arnthorg/FSAE-car-dashboard-/myndir/IMG_20160512_113746.jpg

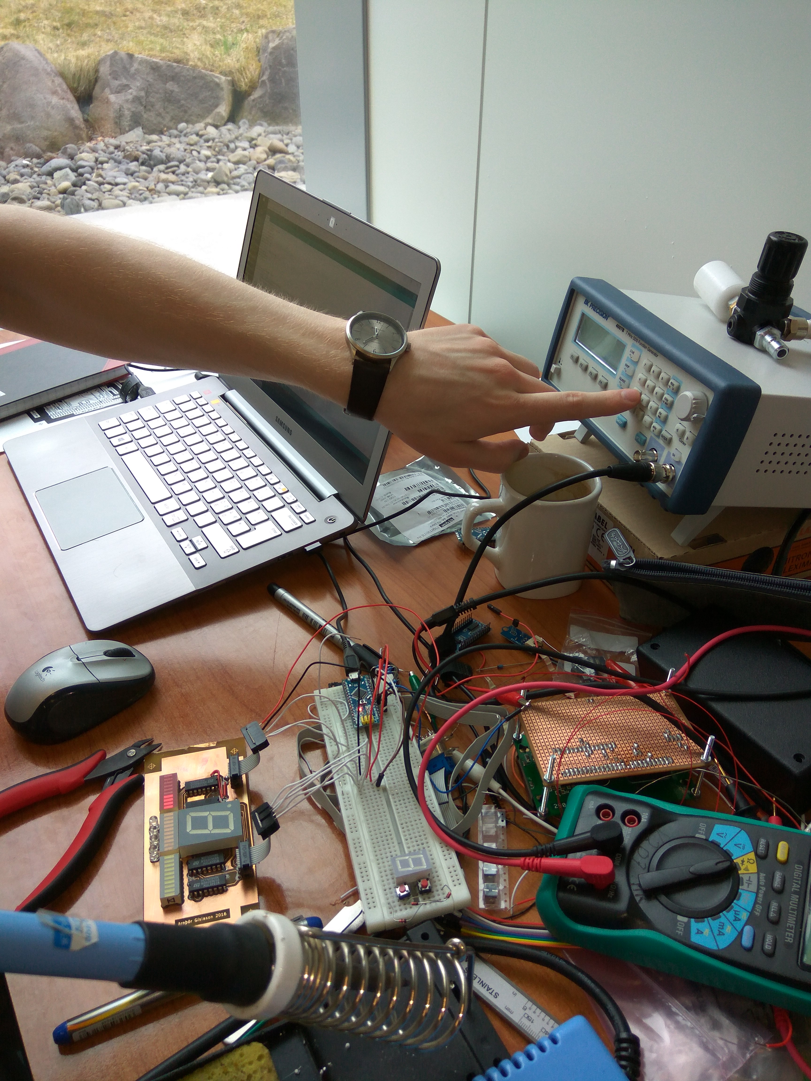
myndir/IMG_20160512_113746.jpg
