arnthorg/FSAE-car-dashboard-/myndir/IMG_20160512_135752.jpg

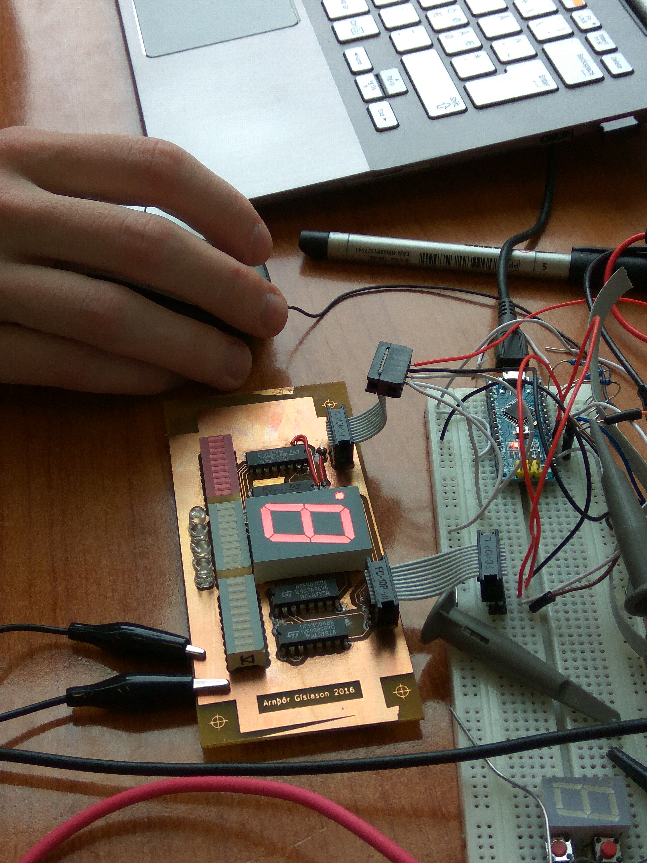
myndir/IMG_20160512_135752.jpg
