arnthorg/FSAE-car-dashboard-/myndir/IMG_20160516_171029.jpg

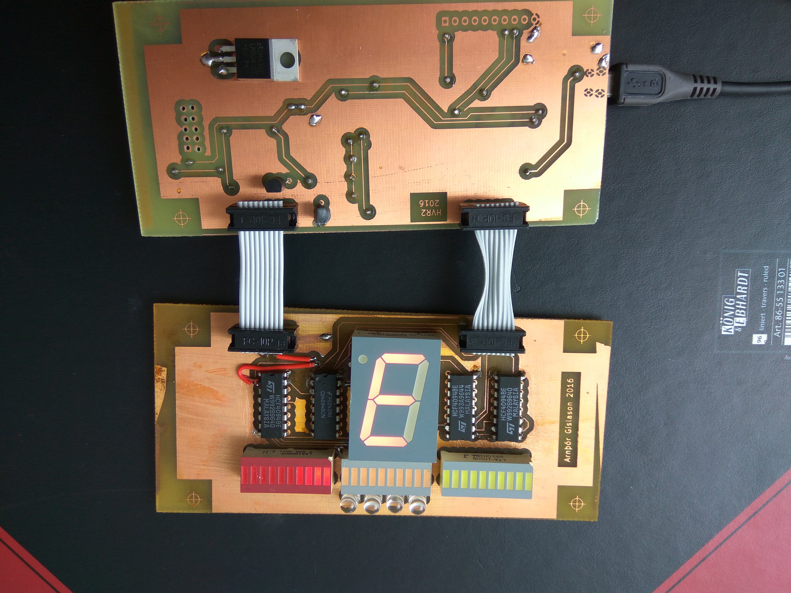
myndir/IMG_20160516_171029.jpg
