arnthorg/FSAE-car-dashboard-/myndir/IMG_20160512_113758.jpg

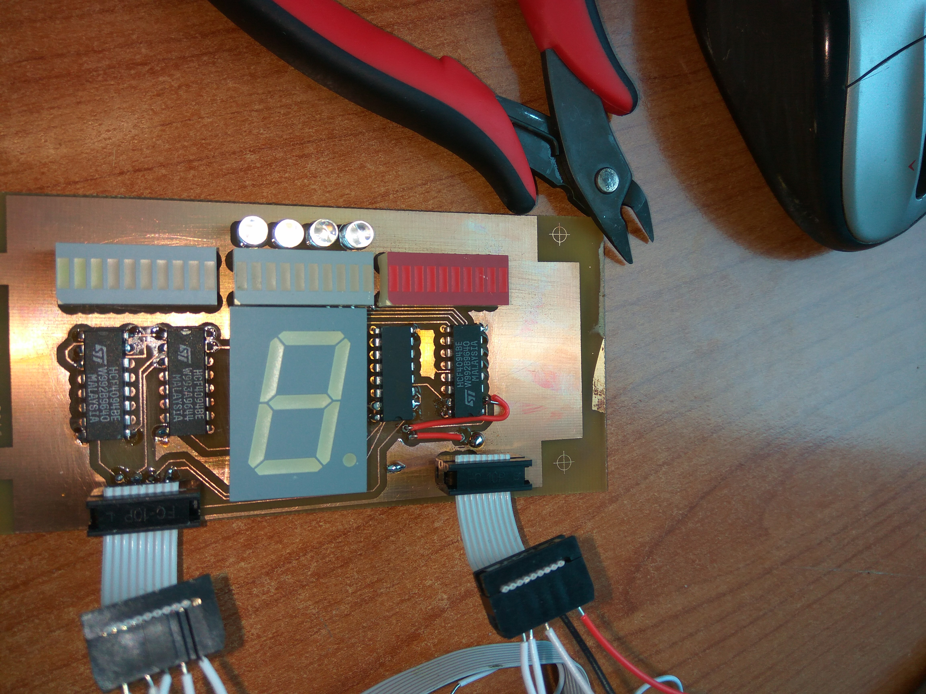
myndir/IMG_20160512_113758.jpg
